maripasa/pocket/Schematics/Pedal.kicad_sch

## KiCad design Schematics/Pedal.kicad_sch (2026-06-23)

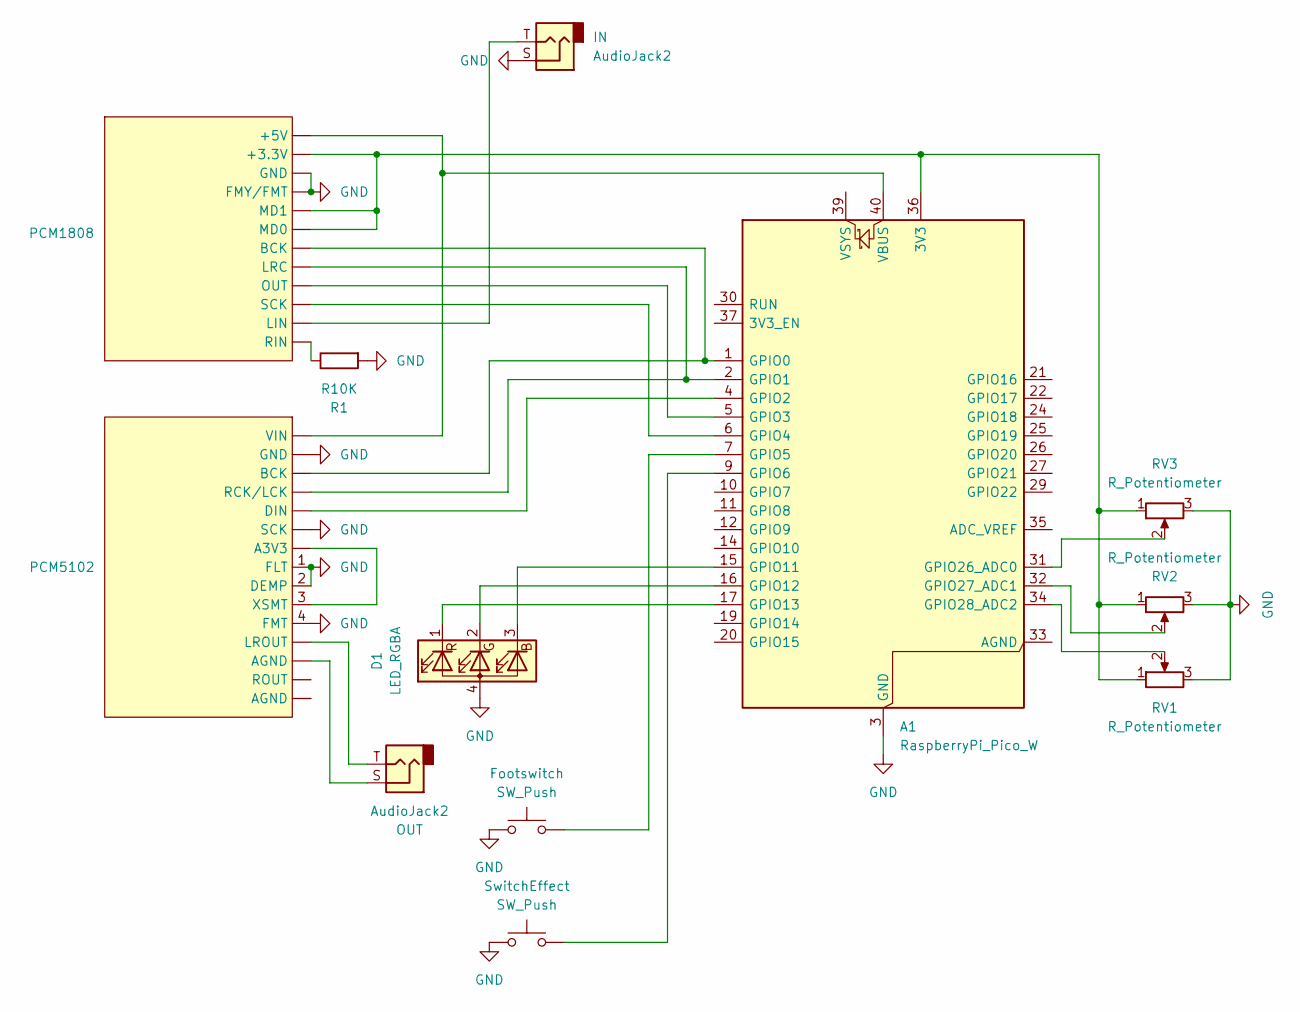
[picture p2: schematic Pedal.kicad_sch]

Parts:
A1: RaspberryPi_Pico_W; RaspberryPi_Pico_W_SMD_HandSolder
D1: LED_RGBA
Footswitch: SW_Push
IN: AudioJack2
OUT: AudioJack2
R1: R10K
RV1, RV2, RV3: R_Potentiometer
SwitchEffect: SW_Push
U1: PCM1808
U2: PCM5102

Connections:
GND: A1.3 (GND), A1.8 (GND), A1.13 (GND), A1.18 (GND), A1.23 (GND), A1.28 (GND), A1.38 (GND), D1.4 (A), Footswitch.1, IN.S, R1.2, RV1.3, RV2.3, RV3.3, SwitchEffect.1, U1., U2. (VIN), U2.1 (FLT), U2.2 (DEMP), U2.4 (FMT)
unnamed: A1.1 (GPIO0), U1., U2. (VIN)
unnamed: A1.2 (GPIO1), U1., U2. (VIN)
unnamed: A1.4 (GPIO2), U2. (VIN)
unnamed: A1.5 (GPIO3), U1.
unnamed: A1.6 (GPIO4), U1.
unnamed: A1.7 (GPIO5), Footswitch.2
unnamed: A1.9 (GPIO6), SwitchEffect.2
unnamed: A1.15 (GPIO11), D1.3 (BK)
unnamed: A1.16 (GPIO12), D1.2 (GK)
unnamed: A1.17 (GPIO13), D1.1 (RK)
unnamed: A1.31 (GPIO26_ADC0), RV3.2
unnamed: A1.32 (GPIO27_ADC1), RV2.2
unnamed: A1.34 (GPIO28_ADC2), RV1.2
unnamed: A1.36 (3V3), RV1.1, RV2.1, RV3.1, U1.
unnamed: A1.40 (VBUS), U1., U2. (VIN)
unnamed: IN.T, U1.
unnamed: OUT.S, U2. (VIN)
unnamed: OUT.T, U2. (VIN)
unnamed: R1.1, U1.
unnamed: U2. (VIN), U2.3 (XSMT)
